SharpCoder/bbot/bbot-models/cosmetic/component-box.SLDPRT

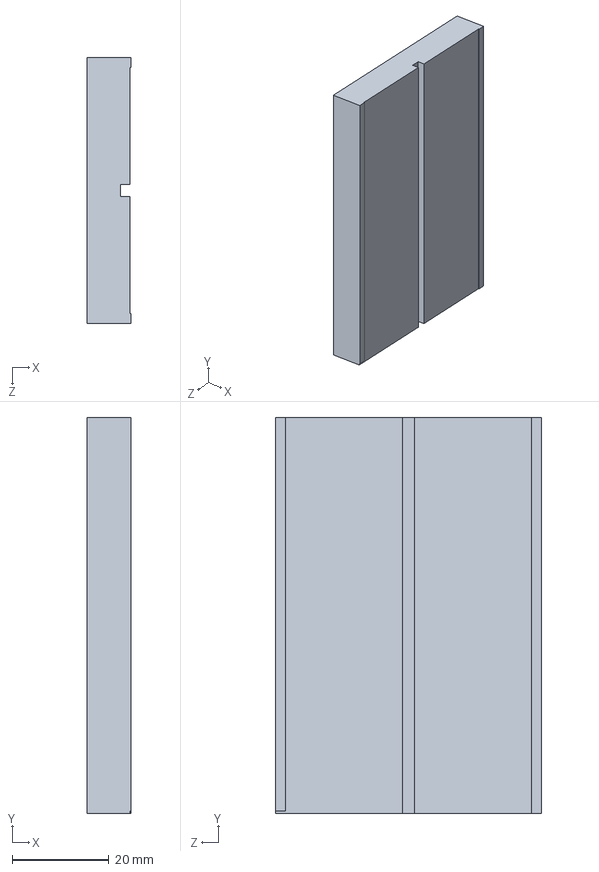
[picture p14: CAD file, 2021-04-06]
bbot-models/cosmetic/component-box.SLDPRT
9.20 x 82.0 x 55.0 mm
